E-Ruhl/ECE_411_Practicum/Photo Documentation/Casing Prototype 4.jpg

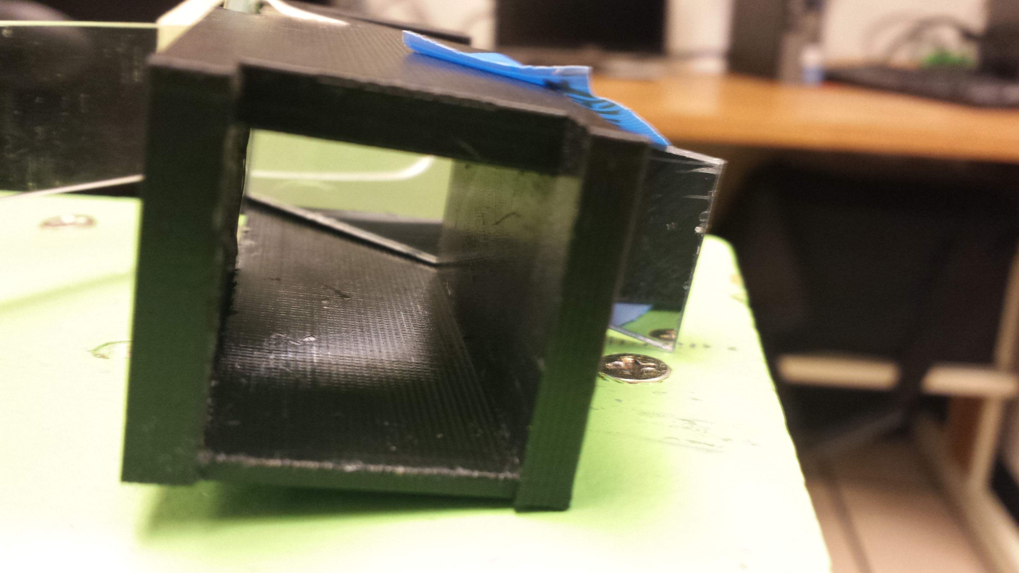
Photo Documentation/Casing Prototype 4.jpg
