E-Ruhl/ECE_411_Practicum/Photo Documentation/First_Working_Prototype.jpg

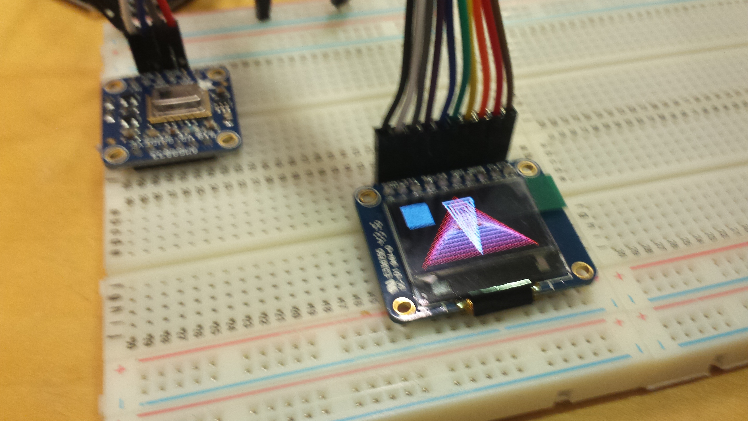
Photo Documentation/First_Working_Prototype.jpg
