E-Ruhl/ECE_411_Practicum/Photo Documentation/Prototype Breadboard Wiring.jpg

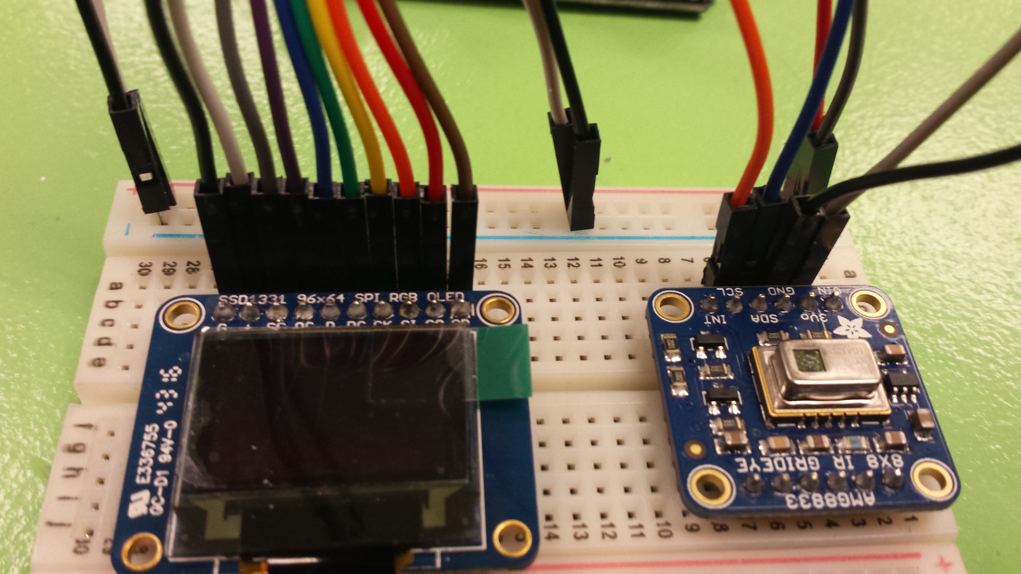
Photo Documentation/Prototype Breadboard Wiring.jpg
